travishoglund/bitcoin-lightning-atm/images/arduino-setup.png

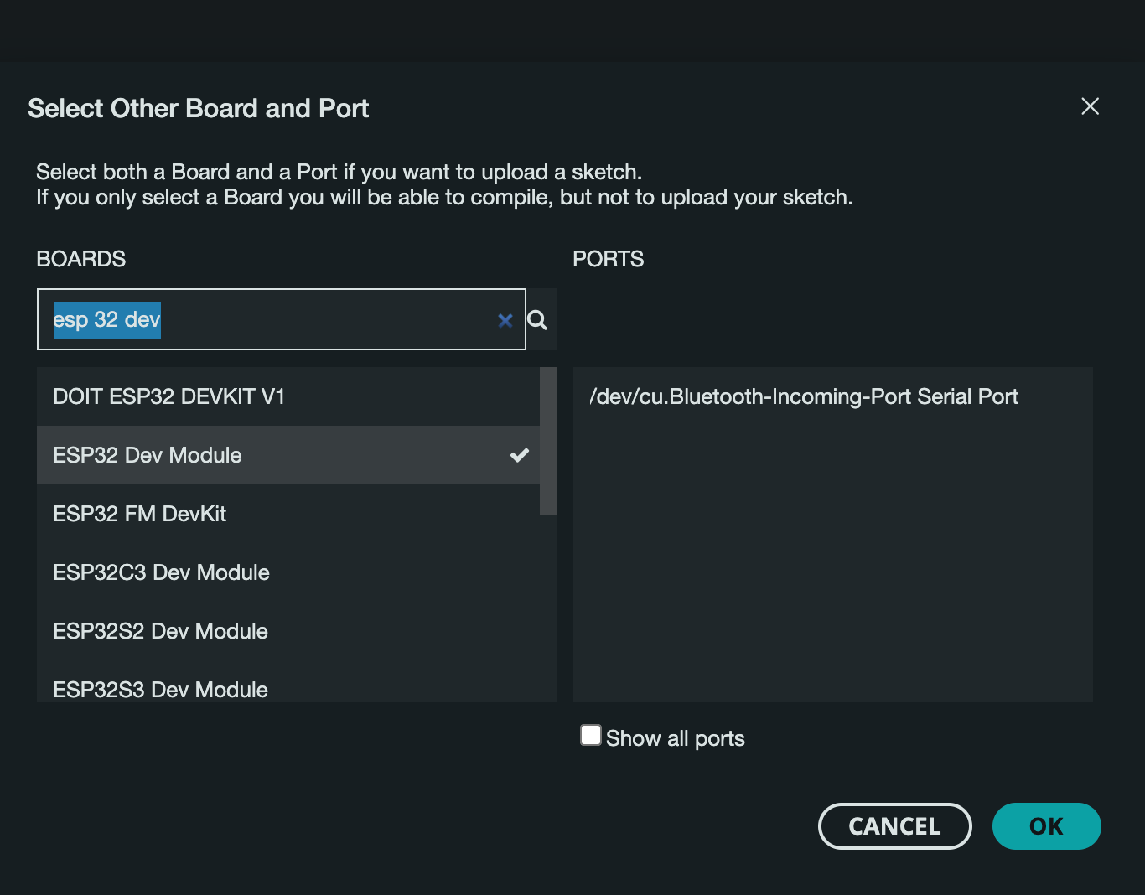
images/arduino-setup.png
