travishoglund/bitcoin-lightning-atm/multi-coin/standard/arduino-code/settings-CAD.ino

String baseURLATM = "https://legend.lnbits.com/lnurldevice/api/v1/lnurl/DEVICE_ID";
String secretATM = "SECRET";
String currencyATM = "CAD";
float coinValues[6] = {0.01, 0.05, 0.10, 0.25, 1.00, 2.00};
int charge = 10; // % you will charge people for service, set in LNbits extension
float maxAmount = 50.00; // max amount per withdraw
